Petros-Kapetanios/Senior-Design/Current_Transformer_test_Board/Current_Transformer_test_Board.kicad_pcb

## KiCad design Current_Transformer_test_Board/Current_Transformer_test_Board.kicad_pcb (2025-04-28)

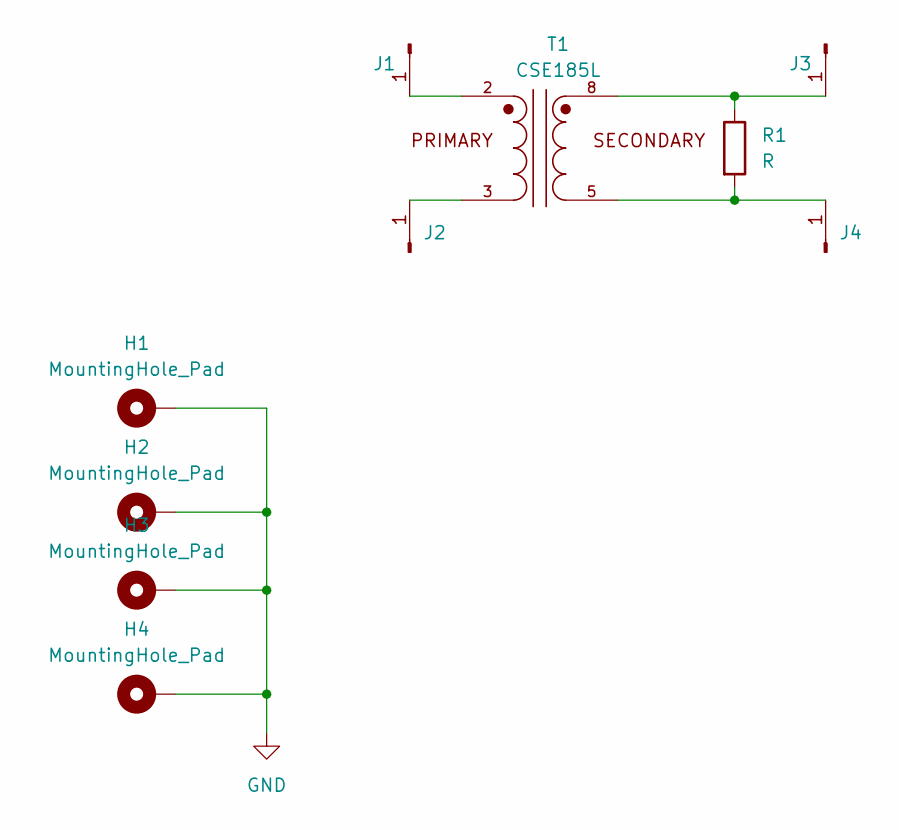
[picture p15: schematic Current_Transformer_test_Board.kicad_sch]

Parts:
H1, H2, H3, H4: MountingHole_Pad; MountingHole_3.2mm_M3_DIN965_Pad_TopBottom
J1, J2, J3, J4: Conn_01x01_Pin; SolderWire-2sqmm_1x01_D2mm_OD3.9mm
R1: R; R_Axial_DIN0207_L6.3mm_D2.5mm_P10.16mm_Horizontal
T1: CSE185L; XFMR_CSE185L; PARTREV N/A

Connections:
GND: H1.1, H2.1, H3.1, H4.1
unnamed: J1.1, T1.2
unnamed: J2.1, T1.3
unnamed: J3.1, R1.1, T1.8
unnamed: J4.1, R1.2, T1.5

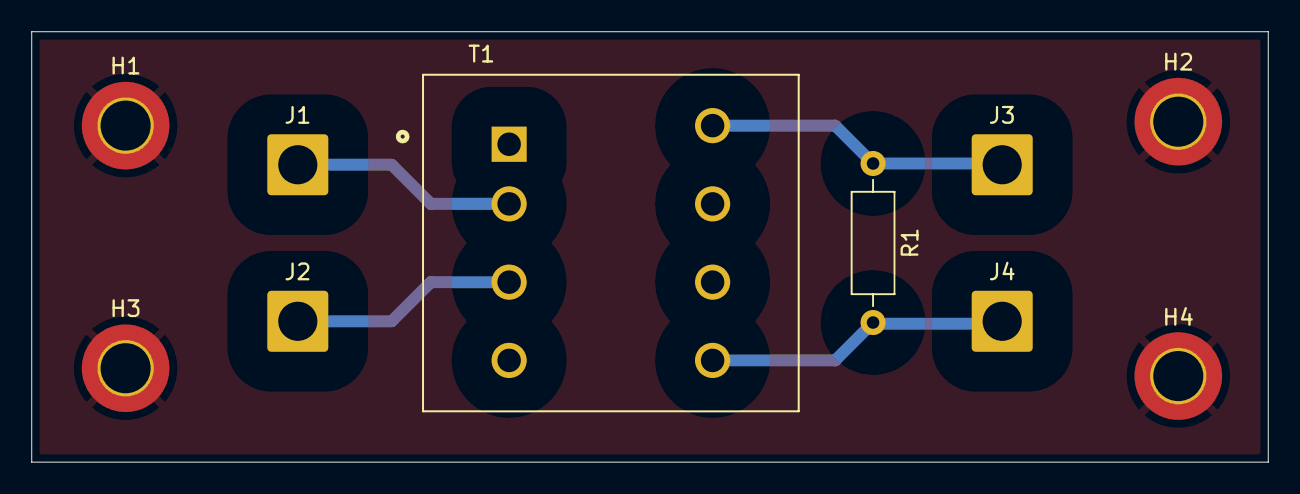
[picture p16: board Current_Transformer_test_Board.kicad_pcb from above]

Board: 2 copper layers, 79.0 x 27.5 mm, 10 parts (0 on the bottom side), 5 nets.
