Petros-Kapetanios/Senior-Design/Capacitor_test_board/(Just In Case)/Capacitor_test_board.kicad_pcb

## KiCad design Capacitor_test_board/(Just In Case)/Capacitor_test_board.kicad_pcb (2025-04-28)

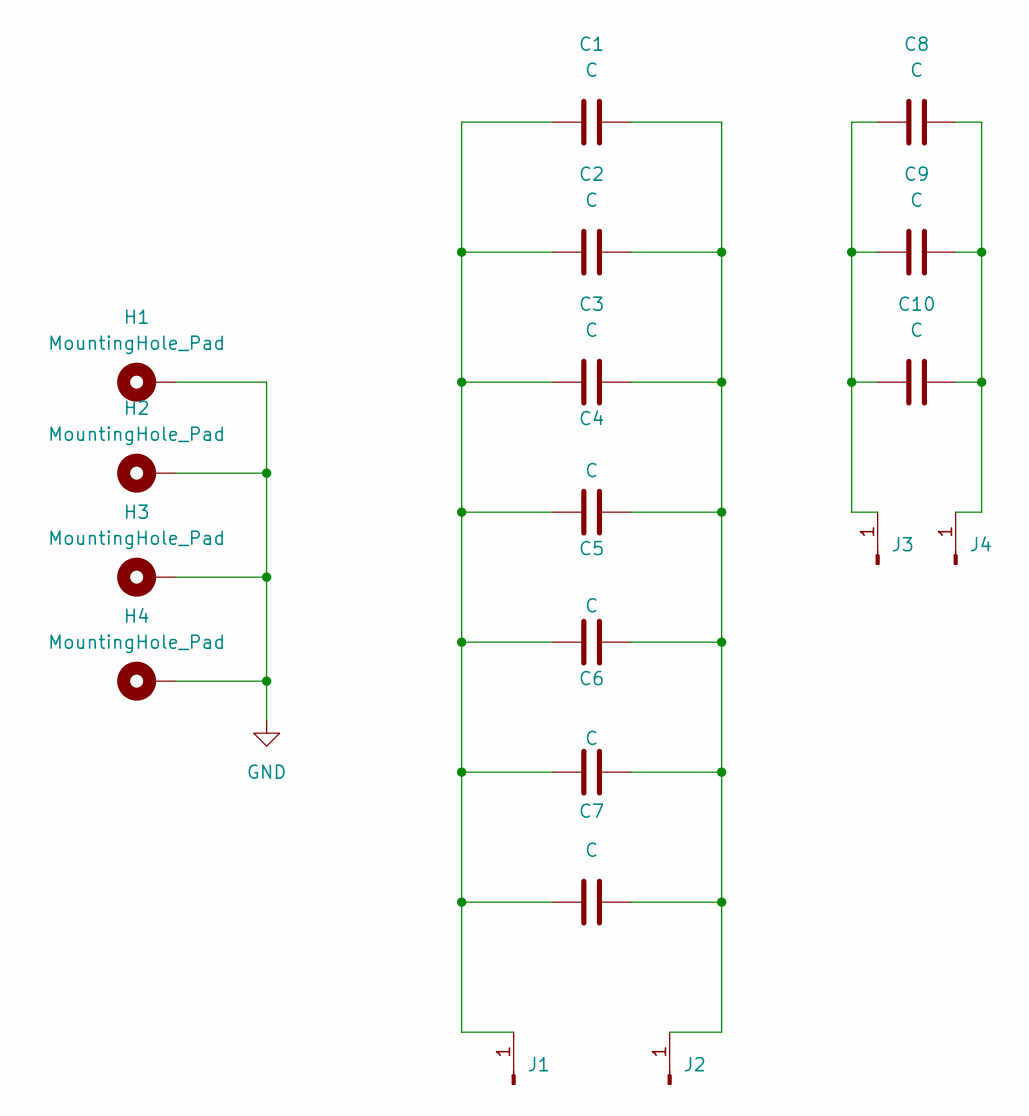
[picture p17: schematic Capacitor_test_board.kicad_sch]

Parts:
C1, C2, C3, C4, C5, C6, C7, C8, C9, C10: C; C_Rect_L24.0mm_W10.9mm_P22.50mm_MKT
H1, H2, H3, H4: MountingHole_Pad; MountingHole_3.2mm_M3_DIN965_Pad_TopBottom
J1, J2, J3, J4: Conn_01x01_Pin; SolderWire-2sqmm_1x01_D2mm_OD3.9mm

Connections:
GND: H1.1, H2.1, H3.1, H4.1
unnamed: C1.1, C2.1, C3.1, C4.1, C5.1, C6.1, C7.1, J1.1
unnamed: C1.2, C2.2, C3.2, C4.2, C5.2, C6.2, C7.2, J2.1
unnamed: C8.1, C9.1, C10.1, J3.1
unnamed: C8.2, C9.2, C10.2, J4.1

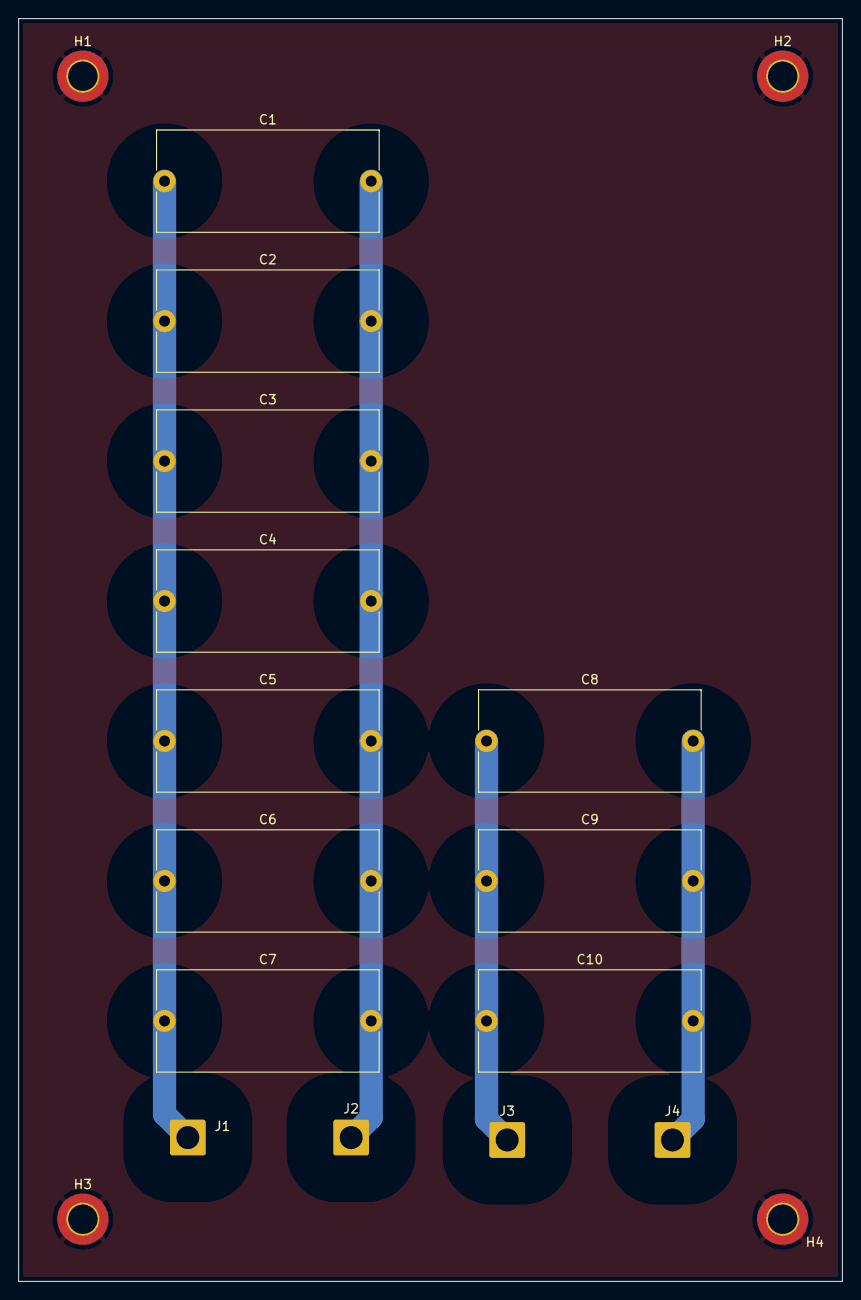
[picture p18: board Capacitor_test_board.kicad_pcb from above]

Board: 2 copper layers, 89.7 x 137.5 mm, 18 parts (0 on the bottom side), 5 nets.
